Rhetticle/UFV/3D Models and STL/Firetruck Head/Firetruck front.stl

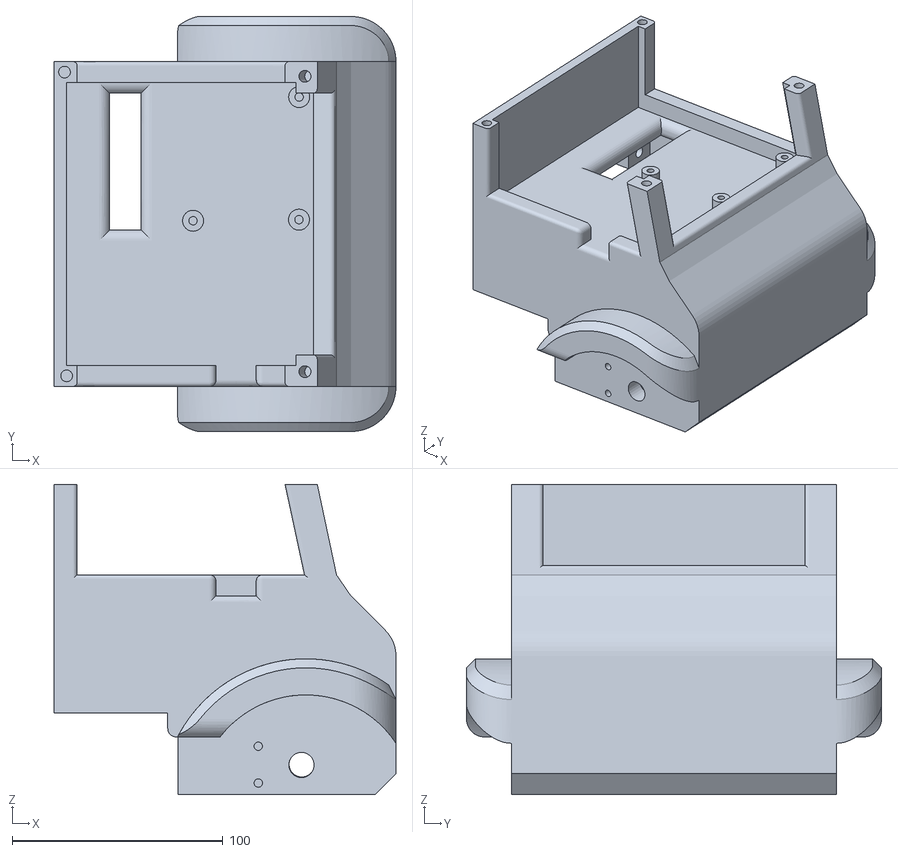
[picture p15: CAD file, 2024-05-05]
3D Models and STL/Firetruck Head/Firetruck front.stl
162.4 x 197.1 x 147.4
