Rhetticle/UFV/3D Models and STL/Pitch stuff/Servo arm.stl

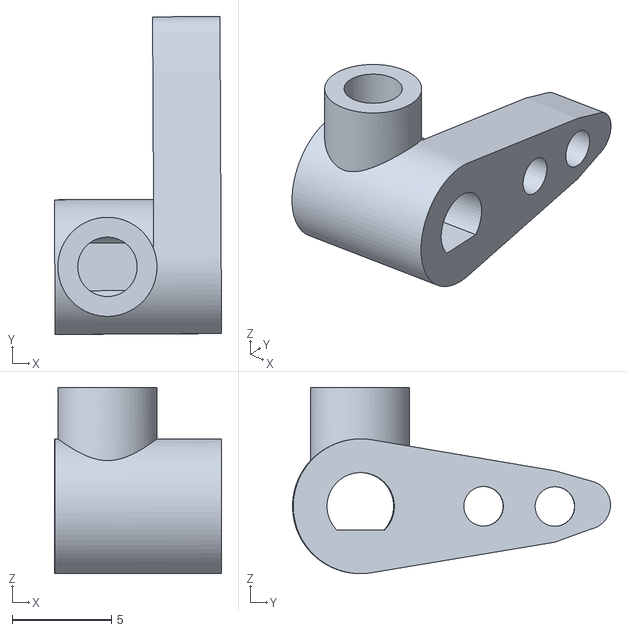
[picture p16: CAD file, 2024-05-05]
3D Models and STL/Pitch stuff/Servo arm.stl
8.44 x 16.0 x 9.40
