Rhetticle/UFV/3D Models and STL/Worm Drive/Worm Wheel.stl

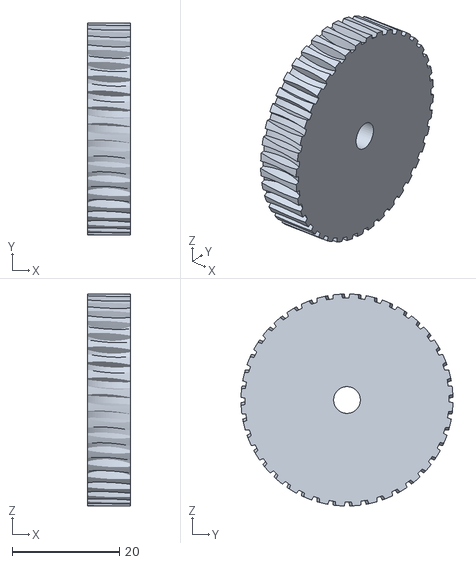
[picture p17: CAD file, 2024-05-05]
3D Models and STL/Worm Drive/Worm Wheel.stl
8.00 x 39.6 x 39.6
