Rhetticle/UFV/3D Models and STL/Worm pitch/Worm wheel.stl

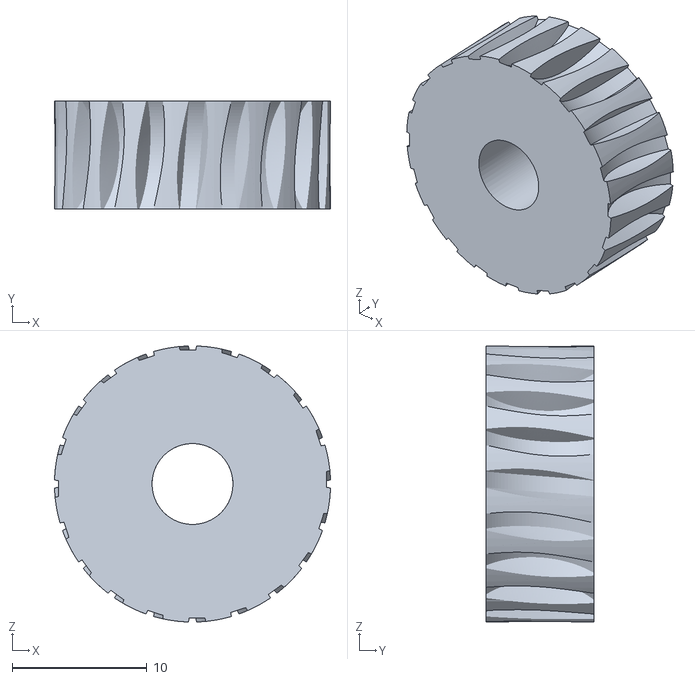
[picture p18: CAD file, 2024-05-05]
3D Models and STL/Worm pitch/Worm wheel.stl
20.5 x 8.00 x 20.5
