Rhetticle/UFV/3D Models and STL/Controller STL/Controller Top.stl

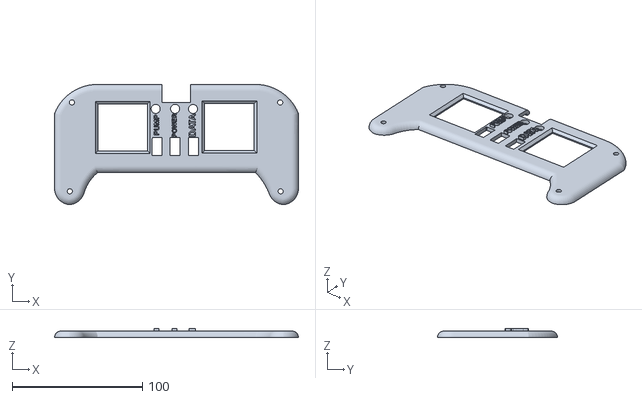
[picture p19: CAD file, 2024-05-05]
3D Models and STL/Controller STL/Controller Top.stl
187.5 x 92.4 x 7.00
