Rhetticle/UFV/3D Models and STL/Firetruck Head/Motor Gear.stl

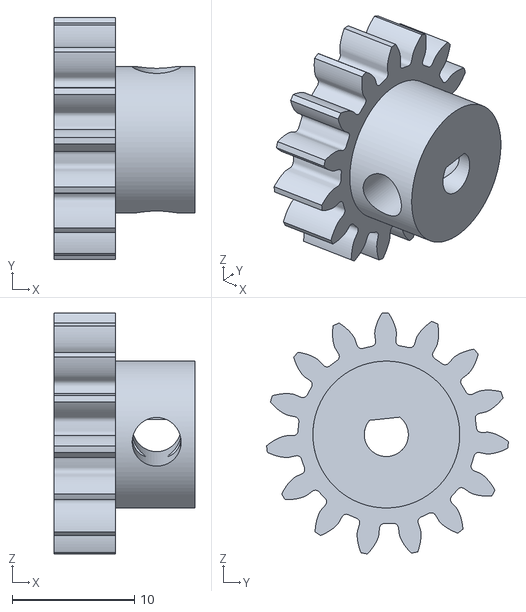
[picture p20: CAD file, 2024-05-05]
3D Models and STL/Firetruck Head/Motor Gear.stl
11.5 x 19.8 x 19.7
