Rhetticle/UFV/3D Models and STL/Pitch stuff/Base ring.stl

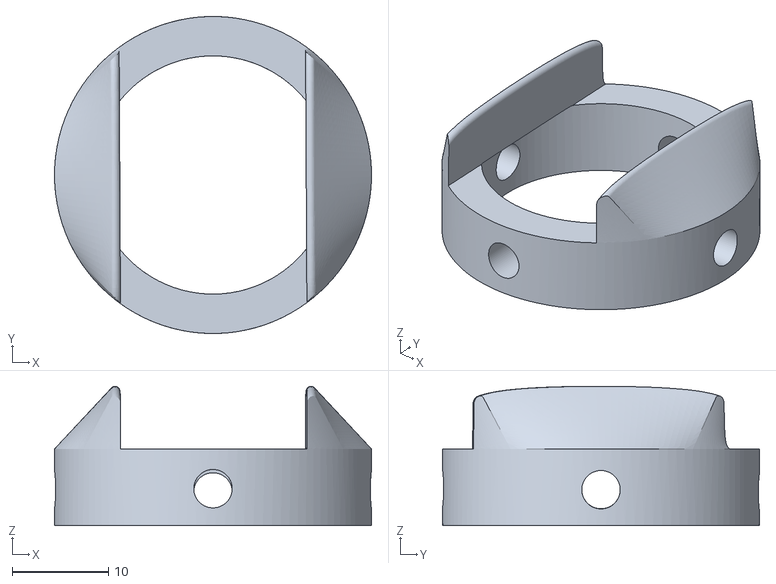
[picture p21: CAD file, 2024-05-05]
3D Models and STL/Pitch stuff/Base ring.stl
33.0 x 33.0 x 14.5
