Rhetticle/UFV/3D Models and STL/Firetruck Head/Platform.stl

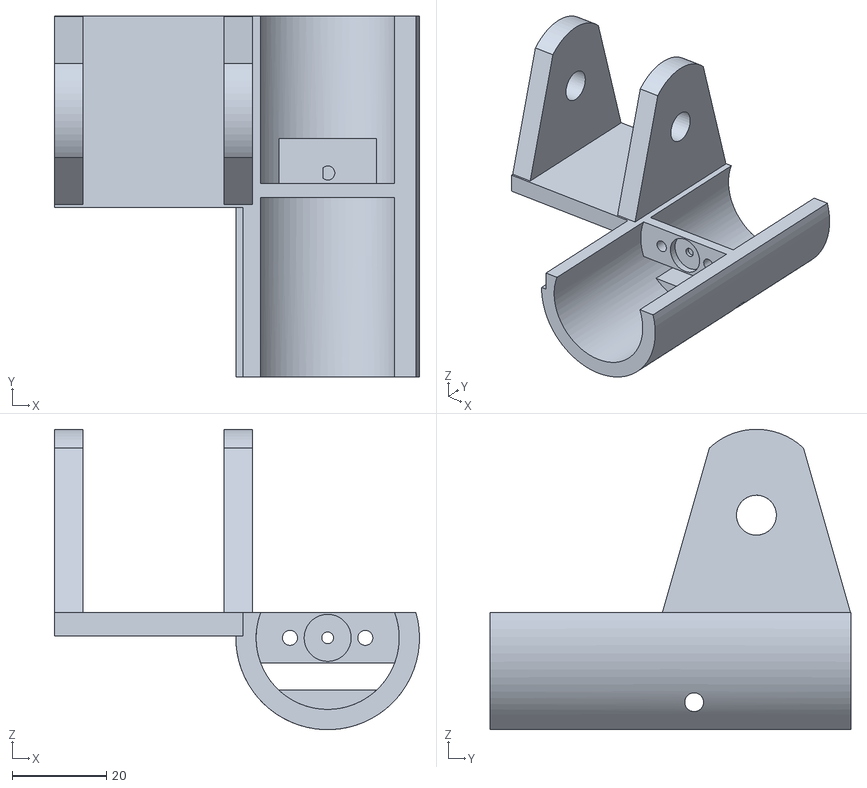
[picture p22: CAD file, 2024-05-05]
3D Models and STL/Firetruck Head/Platform.stl
77.5 x 76.6 x 63.8
