Rhetticle/UFV/3D Models and STL/Firetruck Head/Test Bracket.stl

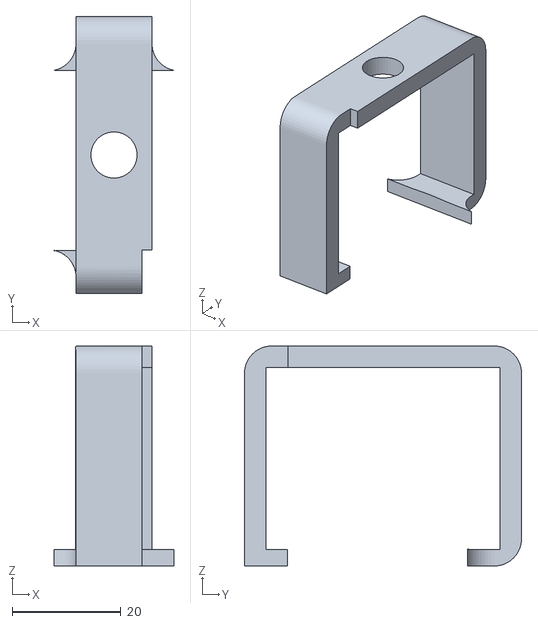
[picture p23: CAD file, 2024-05-05]
3D Models and STL/Firetruck Head/Test Bracket.stl
22.0 x 51.0 x 40.5
