Rhetticle/UFV/3D Models and STL/Firetruck Head/Nozzle Platform.stl

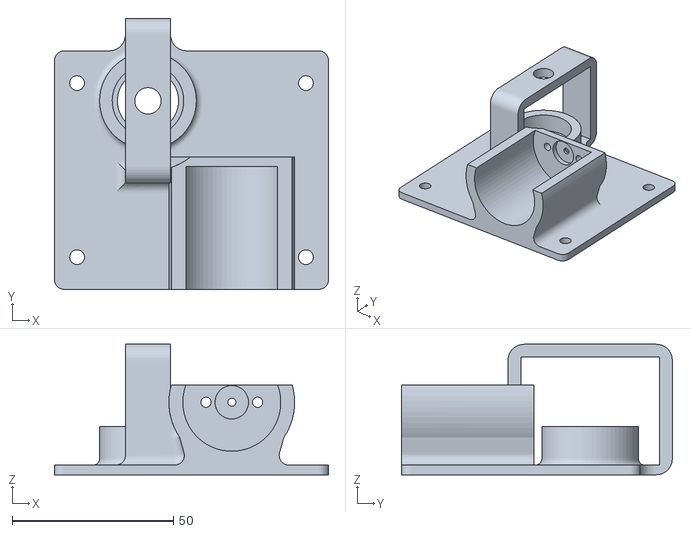
[picture p24: CAD file, 2024-05-05]
3D Models and STL/Firetruck Head/Nozzle Platform.stl
85.0 x 84.0 x 40.5
