Rhetticle/UFV/3D Models and STL/Firetruck Head/Worm Wheel.stl

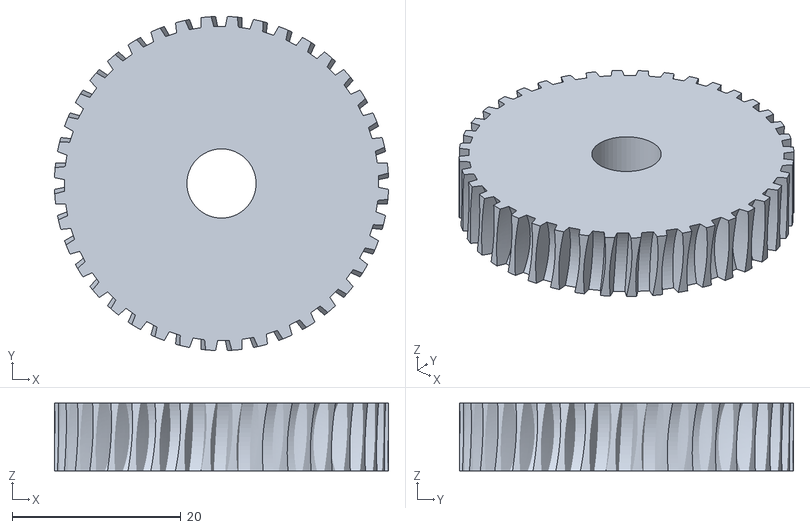
[picture p25: CAD file, 2024-05-05]
3D Models and STL/Firetruck Head/Worm Wheel.stl
39.6 x 39.6 x 8.00
