Rhetticle/UFV/3D Models and STL/Firetruck Head/Guide wheel adapter.stl

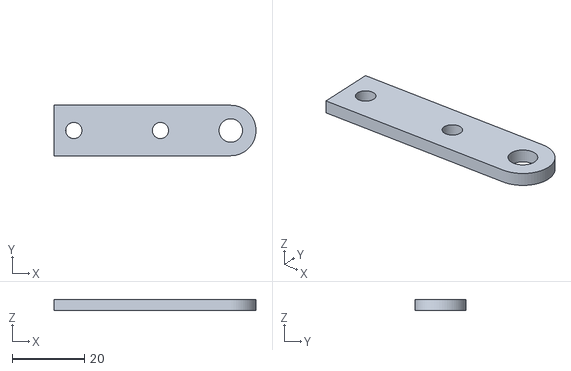
[picture p26: CAD file, 2024-05-05]
3D Models and STL/Firetruck Head/Guide wheel adapter.stl
56.0 x 14.0 x 3.00
