Rhetticle/UFV/3D Models and STL/Firetruck Head/Firetruck back.stl

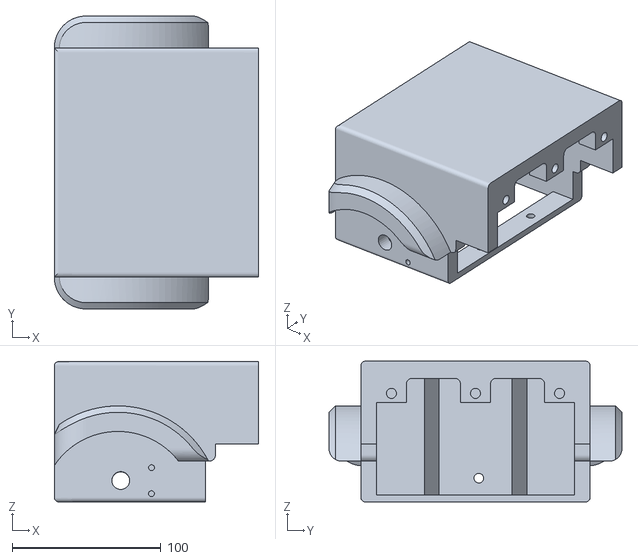
[picture p27: CAD file, 2024-05-05]
3D Models and STL/Firetruck Head/Firetruck back.stl
137.5 x 197.1 x 94.7
