Rhetticle/UFV/3D Models and STL/Firetruck Head/Number Plate.stl

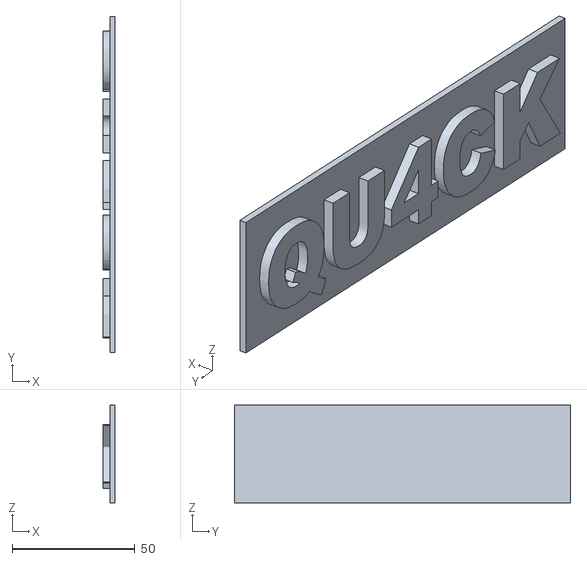
[picture p28: CAD file, 2024-05-05]
3D Models and STL/Firetruck Head/Number Plate.stl
5.00 x 137.0 x 39.8
