Rhetticle/UFV/3D Models and STL/Firetruck Head/Nozzle Gear.stl

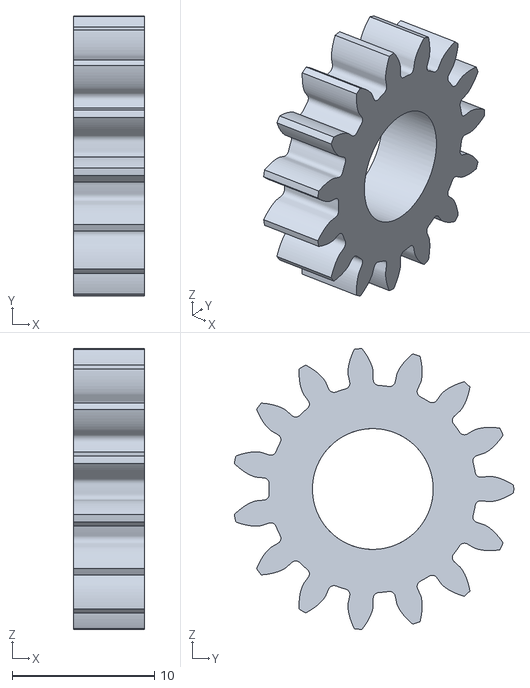
[picture p29: CAD file, 2024-05-05]
3D Models and STL/Firetruck Head/Nozzle Gear.stl
5.00 x 19.7 x 19.8
