Rhetticle/UFV/3D Models and STL/Firetruck Head/Firetruck Head v22.iges

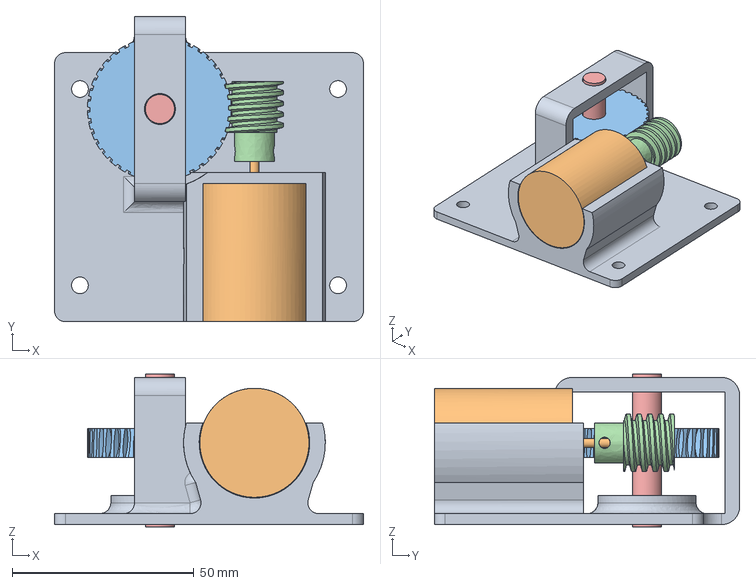
[picture p30: CAD file, 2024-05-05]
3D Models and STL/Firetruck Head/Firetruck Head v22.iges
85.0 x 84.0 x 42.0 mm
